schiad/Rain_bow_clock/Firmware/RainbowClock.X/conf.c

// PIC32MX110F016D Configuration Bit Settings

// 'C' source line config statements

#include <xc.h>

// DEVCFG3
// USERID = No Setting
#pragma config PMDL1WAY = OFF           // Peripheral Module Disable Configuration (Allow multiple reconfigurations)
#pragma config IOL1WAY = OFF            // Peripheral Pin Select Configuration (Allow multiple reconfigurations)
#pragma config FUSBIDIO = OFF           // USB USID Selection (Controlled by Port Function)
#pragma config FVBUSONIO = OFF          // USB VBUS ON Selection (Controlled by Port Function)

// DEVCFG2
#pragma config FPLLIDIV = DIV_4         // PLL Input Divider (4x Divider)
#pragma config FPLLMUL = MUL_16         // PLL Multiplier (16x Multiplier)
#pragma config FPLLODIV = DIV_4         // System PLL Output Clock Divider (PLL Divide by 4)

// DEVCFG1
#pragma config FNOSC = PRIPLL           // Oscillator Selection Bits (Primary Osc w/PLL (XT+,HS+,EC+PLL))
#pragma config FSOSCEN = ON             // Secondary Oscillator Enable (Enabled)
#pragma config IESO = ON                // Internal/External Switch Over (Disabled)
#pragma config POSCMOD = XT             // Primary Oscillator Configuration (XT osc mode)
#pragma config OSCIOFNC = OFF           // CLKO Output Signal Active on the OSCO Pin (Disabled)
#pragma config FPBDIV = DIV_1           // Peripheral Clock Divisor (Pb_Clk is Sys_Clk/8)
#pragma config FCKSM = CSECMD           // Clock Switching and Monitor Selection (Clock Switch Enable, FSCM Enabled)
#pragma config WDTPS = PS8192           // Watchdog Timer Postscaler (1:8192)
#pragma config WINDIS = OFF             // Watchdog Timer Window Enable (Watchdog Timer is in Non-Window Mode)
#pragma config FWDTEN = ON              // Watchdog Timer Enable (WDT Enabled)
#pragma config FWDTWINSZ = WINSZ_25     // Watchdog Timer Window Size (Window Size is 25%)

// DEVCFG0
#pragma config JTAGEN = OFF             // JTAG Enable (JTAG Disabled)
#pragma config ICESEL = ICS_PGx1        // ICE/ICD Comm Channel Select (Communicate on PGEC1/PGED1)
#pragma config PWP = OFF                // Program Flash Write Protect (Disable)
#pragma config BWP = OFF                // Boot Flash Write Protect bit (Protection Disabled)
#pragma config CP = OFF                 // Code Protect (Protection Disabled)
